DangerBirdStrikesAgain/FinalYearDissertation/WriteUp/Dissertation/models.pdf

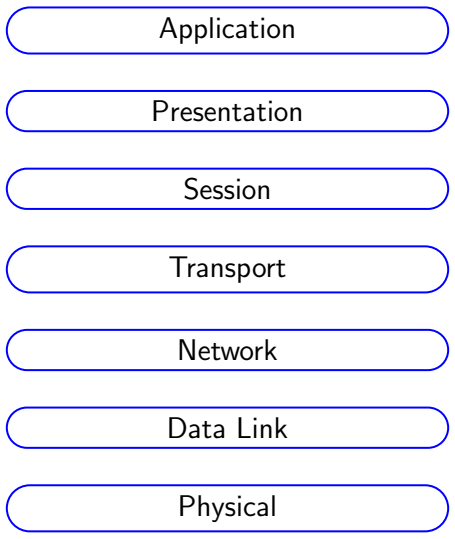
[picture p31: figure]
Application; Presentation; Session; Transport; Network; Data Link; Physical

Figure 1: Open Systems Information (OSI) stack model of network communication

1
