DangerBirdStrikesAgain/FinalYearDissertation/WriteUp/Planning/Phase2 - Alex Riddell-Webster - A MANET to facilitate collision avoidance in rowing boats.pdf

# Part II project - Phase Two Report

## October 7, 2022

## 0 Preliminary Information

Name: Alex Riddell-Webster

College: Murray Edwards

CRSID: ahr38

Director of Studies: Luana Bulat

Supervisor: Matthew Ireland

UTO: Professor Rob Harle has been asked, not confirmed

Title: A MANET to Facilitate Collision Avoidance in Rowing Boats

## 1 Introduction

My project will implement routing in a Mobile Ad-Hoc Network (MANET).

Routing protocols find a path from a source to a destination within the network. Different routing protocols optimise different parameters, and are better suited for various networks [1].

A MANET is characterised by wireless nodes, a frequently changing network topology and no reliance on pre-existing infrastructure. They are decentralised and therefore have no single point of failure [3]. MANETs have a large range of uses, from the military [5] to facilitate communication, to autonomous vehicles
[6] or disaster relief scenarios [7] to gather and move data across locations where previously existing infrastructure has been destroyed.

My project wishes to use a MANET to share a set of locations throughout a set of rowing boats, in order to facilitate collision avoidance. Collisions in rowing can cause damage to both rowers and their equipment. This project’s motivation is to avoid rowing boats colliding with each other and with other obstacles. A radar and AI based obstacle detection system is available [2]. However, to the best of my knowledge, collision avoidance has not been attempted by networking boats together.

In the MANET my project will implement each boat will be a node in the network; storing a set of locations the user should be warned about, and passing these locations throughout the network. The user should be able to add to the list of hazardous locations.

My project will be implemented in hardware, in the real world. In general, networking protocols can be implemented in simulation or in hardware. Depending on the nature of the simulation environment, it might not be possible to use

1

exactly the same code in the simulator as in the real hardware. Due to the time constraints on a Part II Project, I intend to implement my project only in hardware.

## 2 Starting Point

I have a little experience with networking, and routing protocols. My experience is limited to the Part IB networking module, although it is being expanded by the Part II Principles of Communications module. I will need to add to my knowledge of networking and routing protocols.

I have previous experience using Raspberry Pi single-board computers with AdaFruit boards. I have no previous experience with microcontrollers. I will need to improve my knowledge of microcontrollers to complete this project.

## 3 Structure

The first part of the project will be dedicated to research, looking at what routing protocol will be most suited to the network topology rowing boats generate. This phase will also consider whether the whole routing protocol need be implemented for the application. Finally, the research phase will refine the evaluation metrics needed for the project.

After the research phase, I will implement point to point communication between two nodes in hardware.

The next part of the project will implement broadcast and flood routing between at least three nodes.

After a flooding protocol has been implemented, I will use it to implement the secondary routing protocol, decided on in the research stage.

The application layer will then be considered, ensuring that the information passed through the network can be used.

The hardware will then be tested, tweaked and evaluated. Correctness will be evaluated on land, likely in a field, where analysis of the network is easier and larger numbers of metrics can be examined than in the use environment. Performance will be evaluated in the use context - on rowing boats on the water. Evaluation of the network will likely consider the time taken for the network state to be flooded through the nodes, and routing tables then updated, as well as a packet loss ratio [4].

## 4 Success criteria

There are three success criteria I will hold for my project:

1. Flood routing works across the network
2. A point to point routing protocol works across the network
3. The device warns the user when they are approaching a notable location

2

## 5 Extensions

If there is time, I intend to:

1. Review the User Interface (UI) of the device
2. Consider the security of the network
3. If found, consider mitigations for any security flaws in the network

## 6 Plan of Work

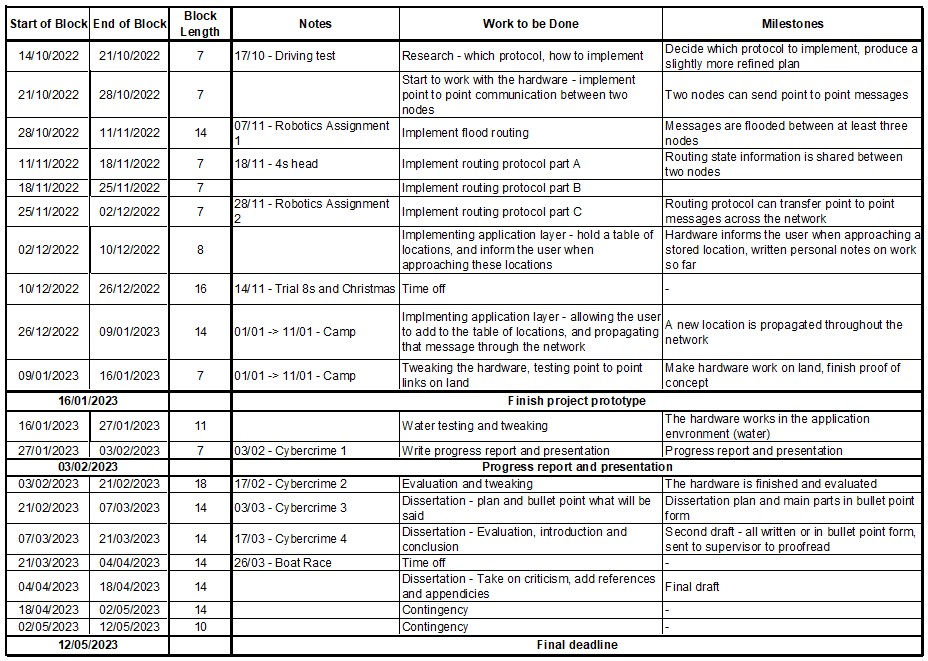
[picture p32: figure]

## 7 Resource Declaration

I plan to use my laptop to implement, evaluate and write up the project. It has a comprehensive system of backups through OneDrive and disk images. A backup of the project will exist with Git version control, hosted on GitHub. My own hardware, including Raspberry Pi Picos, breadboards and AdaFruit radio and GPS modules will be used to develop and implement the project.

Libraries to interface with the AdaFruit boards are written by AdaFruit in Circuit Python, and in my experience tend to be robust, although they occasionally contain bugs. If necessary, I can fork the code and implement bug fixes.

My project will partially rely on the mathematical correctness of routing protocols, work that others have already published.

As the project has a real-world implementation, I have permission from Cambridge University Boat Club to test devices on their boats.

3

## References

[1] 2022 Part II Lecture Notes on Principles of Communications. Crowcroft, J. 2022.
[2] DEVICE | rowcus. https://www.rowcus.com/device. ROWCUS. Re-
trieved 07/10/2022.
[3] Mobile Ad Hoc Networking (MANET): Routing Protocol Performance Issues and Evaluation Considerations. Corson, S. and Macker, J. Network Working Group. 1999.
[4] SERIES Y: GLOBAL INFORMATION INFRASTRUCTURE, INTERNET PROTOCOL ASPECTS AND NEXT-GENERATION NETWORKS Internet protocol aspects – Quality of service and network performance. International Telecommunication Union. 2011.
[5] MILCOM’09: Proceedings of the 28th IEEE conference on Military communications. Richardson, K, Jimenex, C, Stephens D.. 2009.
[6] AD HOC Networks for the Autonomous Car. Davidescu, R, Negrus, E. IOP Conference Series Materials Science and Engineering. 2017.
[7] MANET for Disaster Relief based on NDN. Jin Y., et all. IEEE. 2018.

4
