DangerBirdStrikesAgain/FinalYearDissertation/WriteUp/Planning/Sheet1.pdf

Start of Block | End of Block | Block Length | Notes | Work to be Done | Milestones
14/10/2022 | 21/10/2022 | 7 | | Research - how to implement Epidemic protocol, evaluation methods used for ad-hoc networks | Develop a greater understanding of the Epidemic protocol and a plan for implementing it, create an evaluation plan
21/10/2022 | 28/10/2022 | 7 | | Learning how to use the microcontroller and boards | Ensure all the necessary hardware is available, develop a greater understanding of the Raspberry Pi Pico and CircuitPython
28/10/2022 | 04/11/2022 | 7 | | Start to work with the hardware - implement point to point communication between two nodes | Two nodes can send point to point messages
04/11/2022 | 18/11/2022 | 14 | 07/11 - Robotics Assignment 1 | Implement controlled flood routing | Messages are flooded between at least three nodes
18/11/2022 | 02/12/2022 | 14 | 19/11 - 4s head; 28/11 -Robotics Assignment 2 | Implement Epidemic routing protocol | Routing state information is shared between at least two nodes, Epidemic is implemented
02/12/2022 | 10/12/2022 | 8 | | Test, tweak and debug Epidemic implementation on hardware | Epidemic is implemented on hardware
10/12/2022 | 26/12/2022 | 16 | 14/11 - Trial 8s; Christmas | Time off | -
26/12/2022 | 02/01/2023 | 7 | 01/01 -> 11/01 - Camp | Implementing application layer - read location data from GPS and warn user when approaching known obstacle | The device warns the user when they are approaching a known obstacle
02/01/2023 | 16/01/2023 | 14 | 01/01 -> 11/01 - Camp | Implementing application layer - transfer data between the application and routing layers | The application layer is implemented on hardware
16/01/2023 | 23/01/2023 | 7 | | Tweaking the hardware, testing point to point links on land | The hardware runs on land, finish proof of concept
23/01/2023 | 30/01/2023 | 7 | | Water testing and tweaking | The hardware is implemented and run in the application environment (water)
30/01/2023 | 03/02/2023 | 4 | 03/02 - Cybercrime 1 | Write progress report and presentation | Progress report and presentation
03/02/2023 | | | Progress report and presentation
03/02/2023 | 14/02/2023 | 11 | | Evaluation and tweaking on land | The hardware is evaluated for correctness on land
14/02/2023 | 21/02/2023 | 7 | 17/02 - Cybercrime 2 | Evaluation and tweaking on water | The hardware is evaluated for performance on water
21/02/2023 | 07/03/2023 | 14 | 03/03 - Cybercrime 3 | Dissertation - plan and bullet point what will be said | Dissertation bullet point form (first draft)
07/03/2023 | 21/03/2023 | 14 | 17/03 - Cybercrime 4 | Dissertation - write out preparation and implementation | Dissertation has implementation and preparation written out
21/03/2023 | 04/04/2023 | 14 | 26/03 - Boat Race | Time off | -
04/04/2023 | 18/04/2023 | 14 | | Dissertation - write introduction, conclusion, evaluation | Dissertation fully written, sent to supervisor to proofread (second draft)
18/04/2023 | 02/05/2023 | 14 | | Dissertation - Take on criticism, add references and appendices | Dissertation - final draft
02/05/2023 | 12/05/2023 | 10 | | Contingency | -
12/05/2023 | | | Final deadline

dual core - have threading - research threads in circuit and micropython -- how to get Dates do not include the start of block date but do include the end of block date

If time, just work on the damn application layer

How to evaluate - ITU is super irrelevant bc of the topology
