DangerBirdStrikesAgain/FinalYearDissertation/WriteUp/Planning/StateMachinesAndDataStructures.pdf

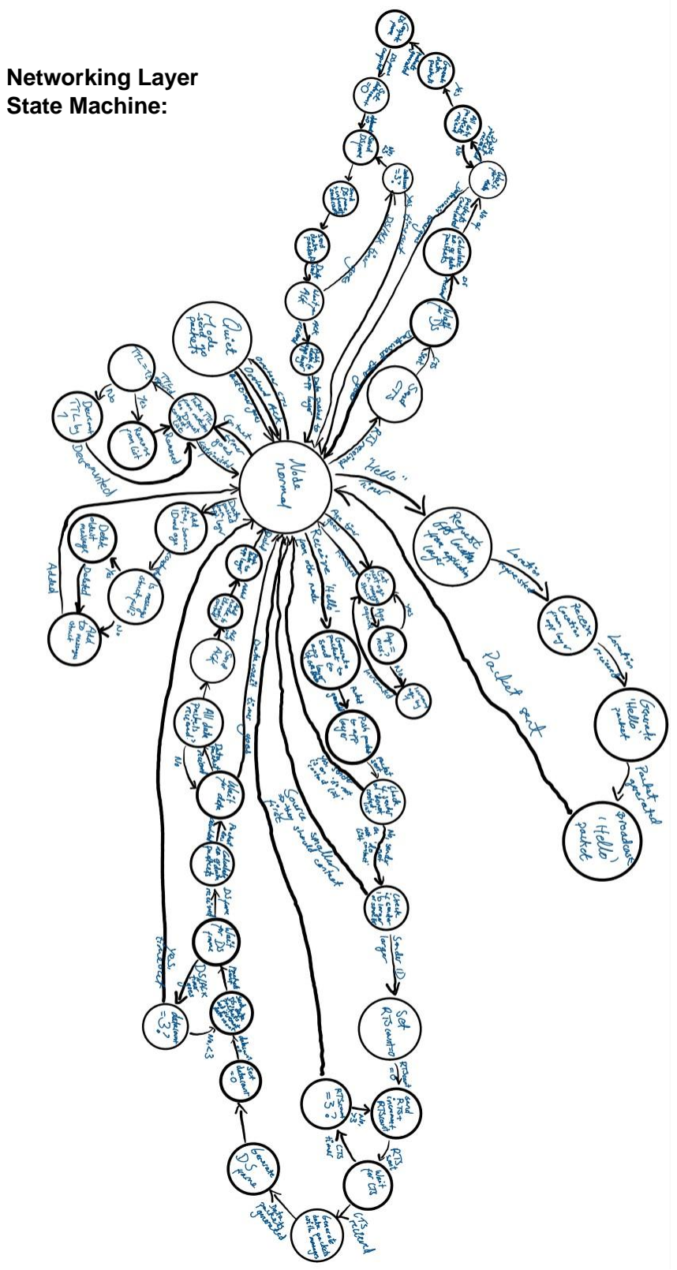
[picture p36: page 1]

Networking Layer
State Machine:

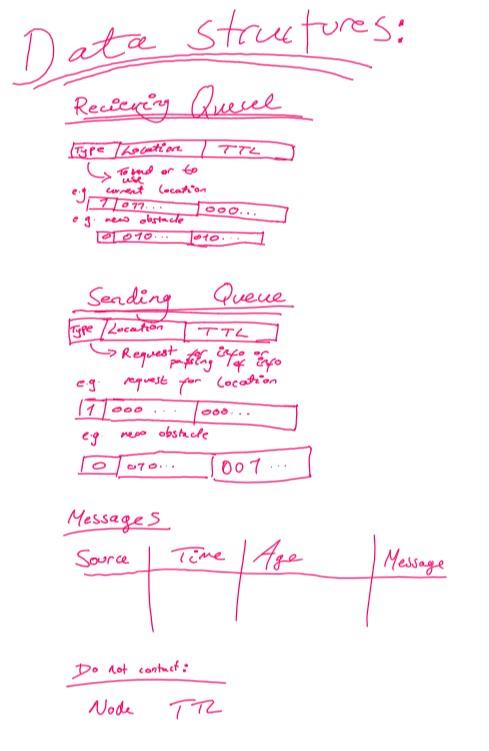
[picture p37: figure]

Networking Layer Data Structures:

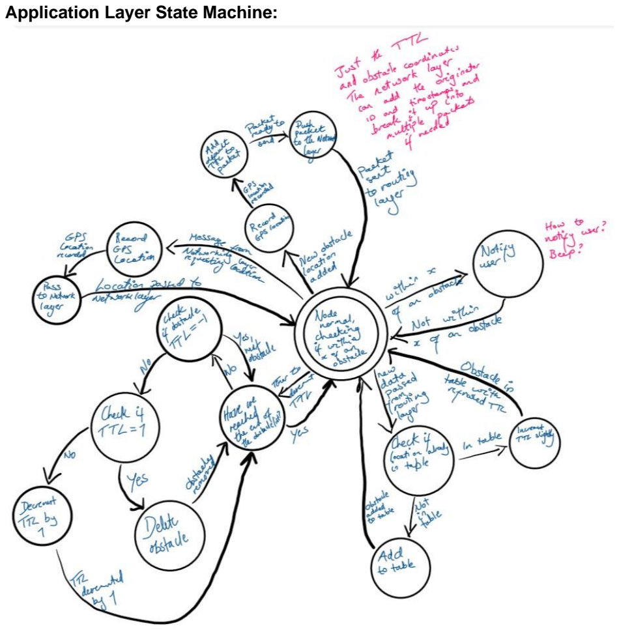
[picture p38: page 3]

Application Layer State Machine:

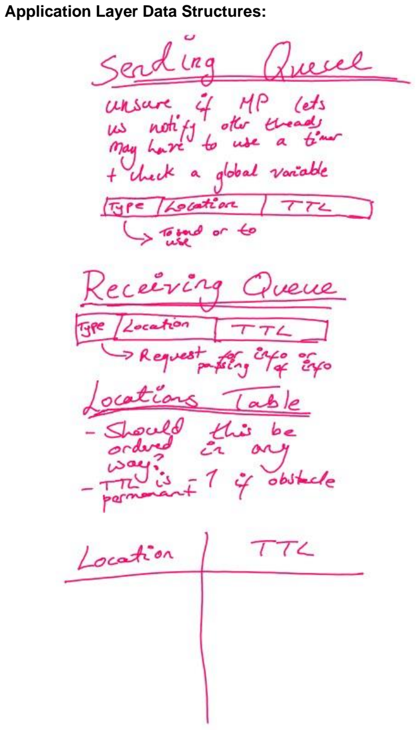
[picture p39: page 4]

Application Layer Data Structures:
