DangerBirdStrikesAgain/FinalYearDissertation/WriteUp/Planning/ApplicationLayerDataStructures.jpg

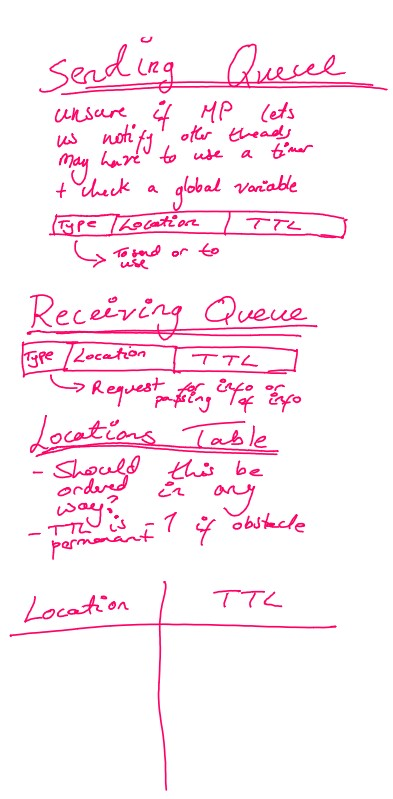
WriteUp/Planning/ApplicationLayerDataStructures.jpg
