DangerBirdStrikesAgain/FinalYearDissertation/WriteUp/Planning/ApplicationStateMachine.jpg

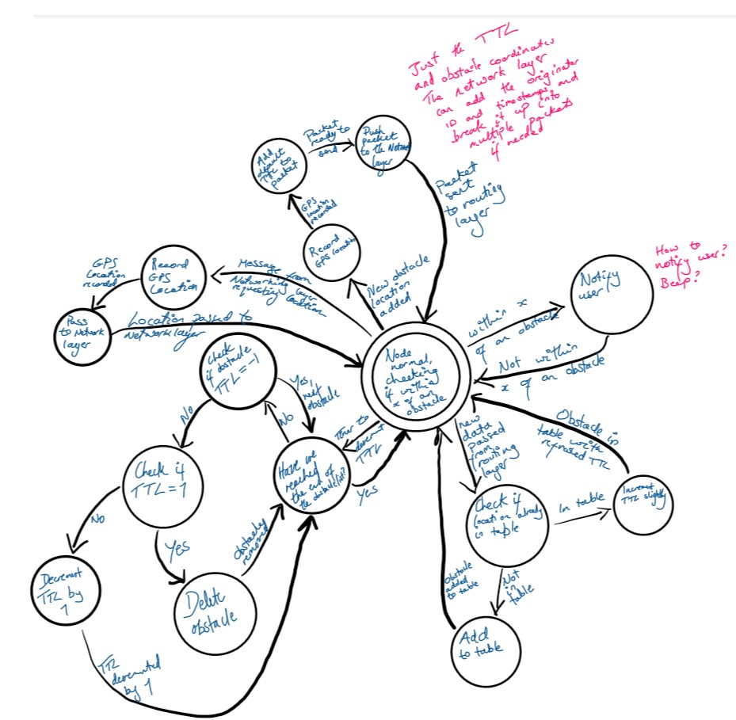
WriteUp/Planning/ApplicationStateMachine.jpg
