DangerBirdStrikesAgain/FinalYearDissertation/WriteUp/Planning/FloodRoutingStateMachine.jpg

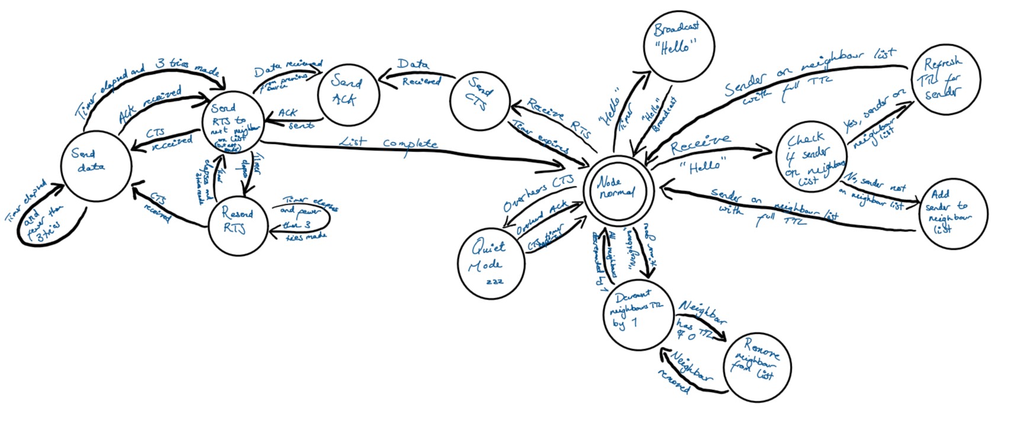
WriteUp/Planning/FloodRoutingStateMachine.jpg
