DangerBirdStrikesAgain/FinalYearDissertation/2347C/Development/Misc/GPS/GPSTestCircuitPython.py

"""
Check that the adafruit ultimate GPS breakout V3 working

Wiring:
GPS    Pico
-----------
GND -> GND
VIN -> 3V3
RX  -> GP4
TX  -> GP5
"""

import time
import board
import busio
import digitalio
import adafruit_gps


def toCoords(deg, min):
    return(float(f"{deg}.{str(min).replace(".", "")}"))
        
        

uart = busio.UART(board.GP4, board.GP5, baudrate=9600, timeout=10)
gps = adafruit_gps.GPS(uart, debug=False)  # Use UART/pyserial

# Turn on the basic GGA and RMC info (what you typically want)
#gps.send_command(b"PMTK314,0,1,0,1,0,0,0,0,0,0,0,0,0,0,0,0,0,0,0")
# Turn on everything
gps.send_command(b'PMTK314,1,1,1,1,1,1,0,0,0,0,0,0,0,0,0,0,0,0,0')


# Set update rate to once a second (1hz) which is what you typically want.
print(gps.send_command(b"PMTK220,1000"))
# Or decrease to once every two seconds by doubling the millisecond value.
# Be sure to also increase your UART timeout above!

while True:
    if gps.update():
    # Every second print out current location details if there's a fix.
        if not gps.has_fix or gps.timestamp_utc is None:
            print("Waiting for fix... ")
            continue
        
        # We have a fix! (gps.has_fix is true)
        print("=" * 40)  # Print a separator line.
        print(
            "Fix timestamp: {}/{}/{} {:02}:{:02}:{:02}".format(
                gps.timestamp_utc.tm_mon,  # Grab parts of the time from the
                gps.timestamp_utc.tm_mday,  # struct_time object that holds
                gps.timestamp_utc.tm_year,  # the fix time.  Note you might
                gps.timestamp_utc.tm_hour,  # not get all data like year, day,
                gps.timestamp_utc.tm_min,  # month!
                gps.timestamp_utc.tm_sec,
            )
        )
        
        print(f"Latitude: {gps.latitude_degrees}.{str(gps.latitude_minutes).replace(".", "")}")
        print(f"Longitude: {gps.longitude_degrees}.{str(gps.longitude_minutes).replace(".", "")}")
        
        """
        print("Latitude: {0:.6f} degrees".format(gps.latitude))
        print("Longitude: {0:.6f} degrees".format(gps.longitude))
        print(
            "Precise Latitude: {:2.}{:2.4f} degrees".format(
                gps.latitude_degrees, gps.latitude_minutes
            )
        )
        print(
            "Precise Longitude: {:2.}{:2.4f} degrees".format(
                gps.longitude_degrees, gps.longitude_minutes
            )
        )
        print("Fix quality: {}".format(gps.fix_quality))
        # Some attributes beyond latitude, longitude and timestamp are optional
        # and might not be present.  Check if they're None before trying to use!
        if gps.satellites is not None:
            print("# satellites: {}".format(gps.satellites))
        if gps.altitude_m is not None:
            print("Altitude: {} meters".format(gps.altitude_m))
        if gps.speed_knots is not None:
            print("Speed: {} knots".format(gps.speed_knots))
        if gps.track_angle_deg is not None:
            print("Track angle: {} degrees".format(gps.track_angle_deg))
        if gps.horizontal_dilution is not None:
            print("Horizontal dilution: {}".format(gps.horizontal_dilution))
        if gps.height_geoid is not None:
            print("Height geoid: {} meters".format(gps.height_geoid))
            """
